KilianKlepper/SCRIPTFlutist/App/Assets/Example_2.jpg

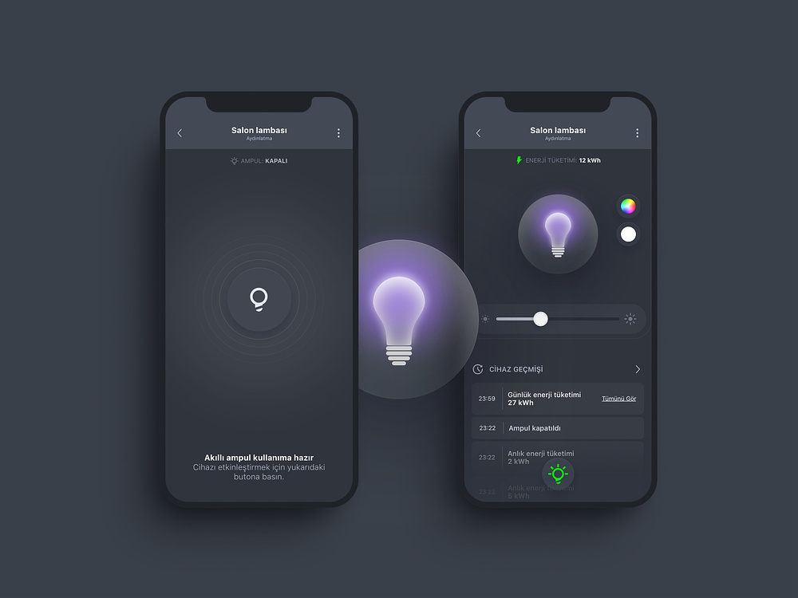
App/Assets/Example_2.jpg
